Stawberrymind/bubbl/Assets/case_front_back.png

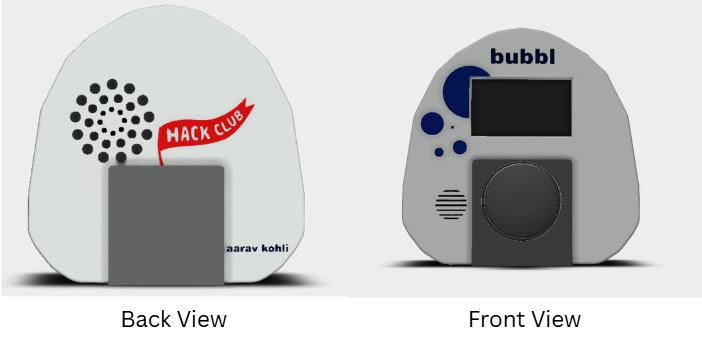
Assets/case_front_back.png
