Stawberrymind/bubbl/Assets/assembly_3.png

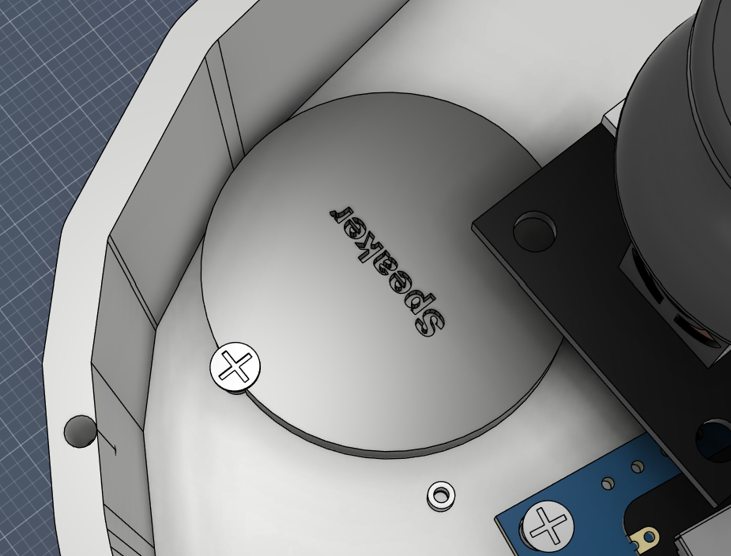
Assets/assembly_3.png
