Stawberrymind/bubbl/Assets/assembly_4.png

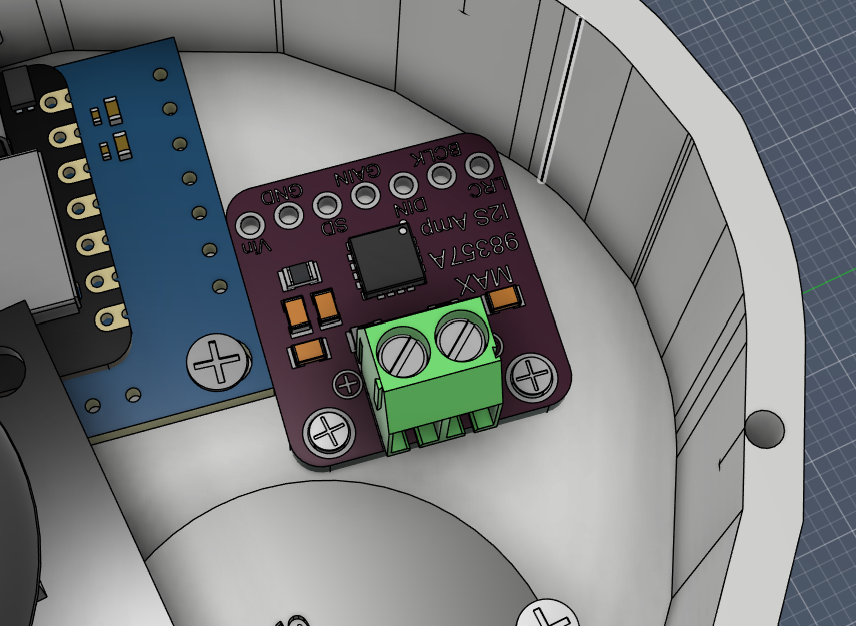
Assets/assembly_4.png
