Stawberrymind/bubbl/Assets/assembly_5.png

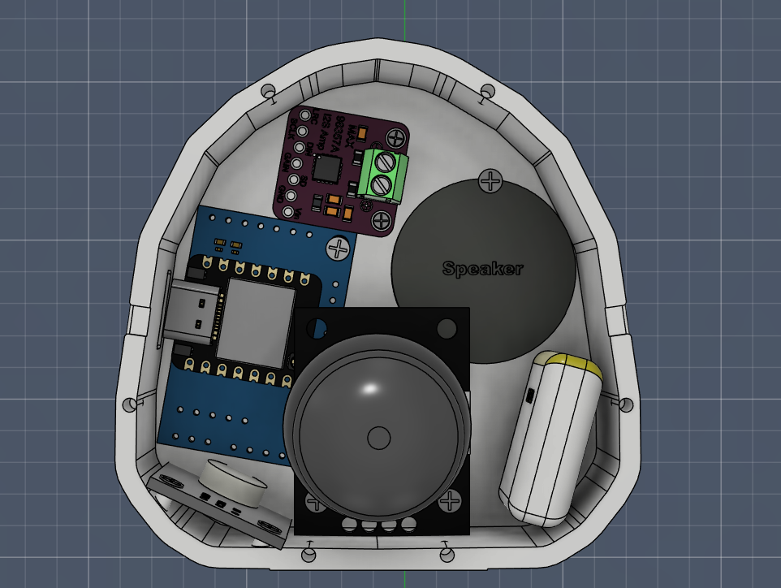
Assets/assembly_5.png
