Stawberrymind/bubbl/Assets/assembly_6.png

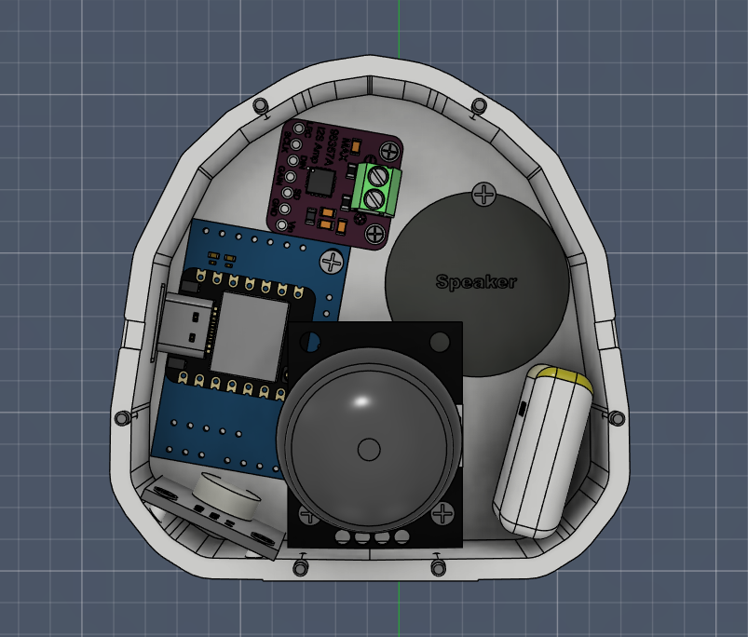
Assets/assembly_6.png
