Stawberrymind/bubbl/Assets/assembly_7.png

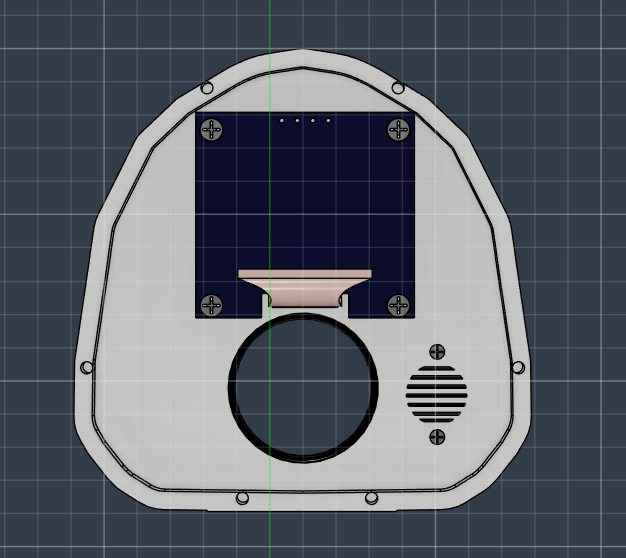
Assets/assembly_7.png
