Stawberrymind/bubbl/Assets/assembly_8.png

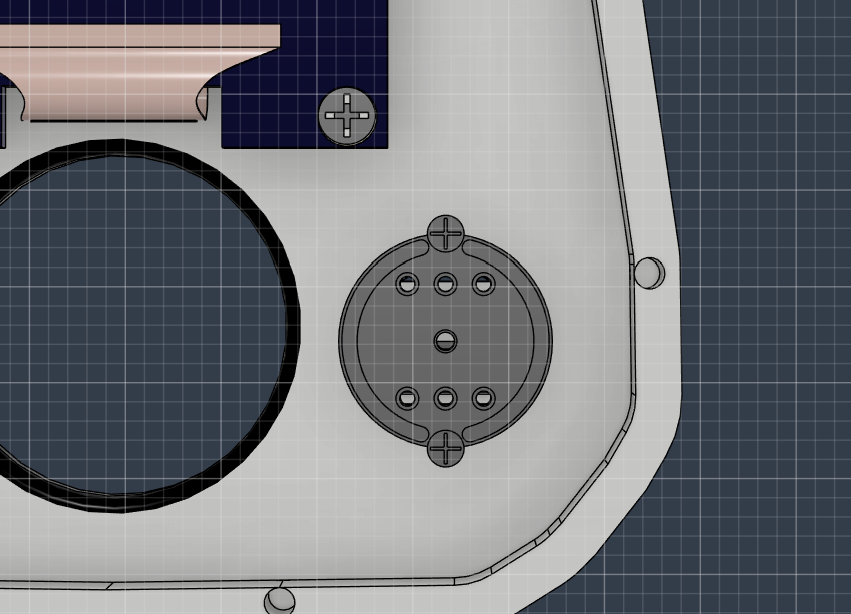
Assets/assembly_8.png
