Stawberrymind/bubbl/Assets/bubbl_assembled.png

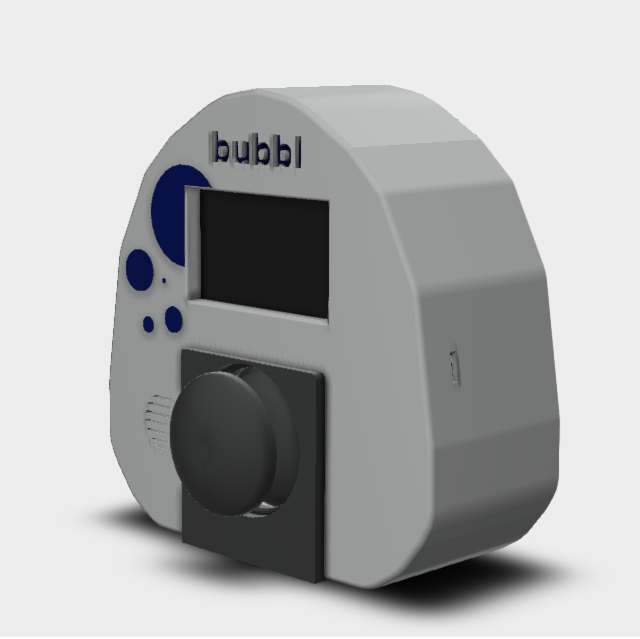
Assets/bubbl_assembled.png
