Stawberrymind/bubbl/Assets/wiring_diagram.png

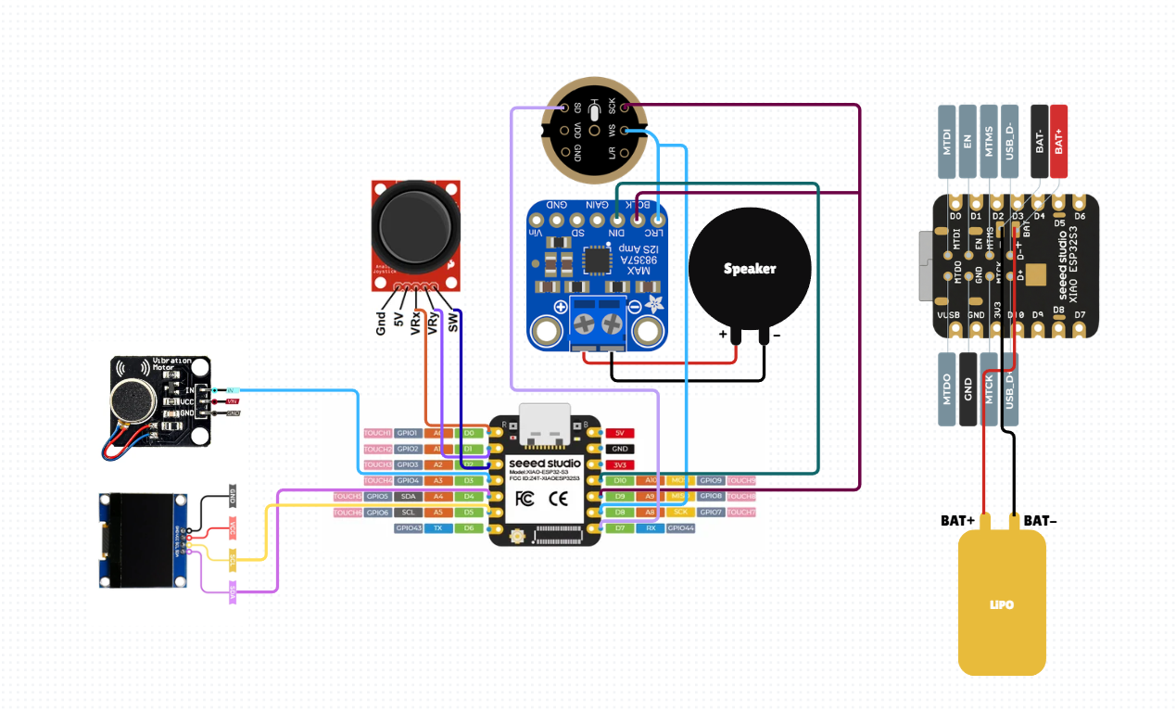
Assets/wiring_diagram.png
